dymczykm/7909_dcdc_converter/ltspice/lt3471.asc

C1: cap; 22µ; Rser=0 Lser=0 mfg="Murata" pn="GCM32ER71C226ME19" type="X7R"
C2: cap; 100n; Rser=16.9m Lser=332p mfg="Würth Elektronik" pn="885012205037 WCAP-CSGP 0402" type="X7R"
C3: cap; 22µ; Rser=0 Lser=0 mfg="Murata" pn="GCM32ER71C226ME19" type="X7R"
C4: cap; 22µ; Rser=0 Lser=0 mfg="Murata" pn="GCM32ER71C226ME19" type="X7R"
C5: cap; 150p; Rser=110.8m Lser=560p mfg="Würth Elektronik" pn="885012006024 WCAP-CSGP 0603" type="NP0"
C6: cap; 22µ; Rser=0 Lser=0 mfg="Murata" pn="GCM32ER71C226ME19" type="X7R"
C7: cap; 10n; Rser=55.4m Lser=199p mfg="Würth Elektronik" pn="885012205031 WCAP-CSGP 0402" type="X7R"
C8: cap; 22µ; Rser=0 Lser=0 mfg="Murata" pn="GCM32ER71C226ME19" type="X7R"
C9: cap; 150p; Rser=110.8m Lser=560p mfg="Würth Elektronik" pn="885012006024 WCAP-CSGP 0603" type="NP0"
C10: cap; 22µ; Rser=0 Lser=0 mfg="Murata" pn="GCM32ER71C226ME19" type="X7R"
C11: cap; 10n; Rser=55.4m Lser=199p mfg="Würth Elektronik" pn="885012205031 WCAP-CSGP 0402" type="X7R"
D1: schottky; MBRS130L
D2: schottky; MBRS130L
L1: ind; 10µ; Ipk=3 Rser=84m Rpar=942 Cpar=0 mfg="Coilcraft" pn="XAL4040-103"
L2: ind; 33µ; Ipk=1.2 Rser=223.6m Rpar=3.109K Cpar=0 mfg="Coilcraft" pn="LPS6225-333"
L3: ind; 33µ; Ipk=1.2 Rser=223.6m Rpar=3.109K Cpar=0 mfg="Coilcraft" pn="LPS6225-333"
L4: ind; 33µ; Ipk=1.2 Rser=223.6m Rpar=3.109K Cpar=0 mfg="Coilcraft" pn="LPS6225-333"
L5: ind; 22µ; Ipk=970m Rser=156.52m Rpar=2.072K Cpar=0 mfg="Coilcraft" pn="MOS6020-223"
L6: ind; 15µ; Ipk=2.8 Rser=109m Rpar=1.413K Cpar=0 mfg="Coilcraft" pn="XAL4040-153"
L7: ind; 33µ; Ipk=1.2 Rser=223.6m Rpar=3.109K Cpar=0 mfg="Coilcraft" pn="LPS6225-333"
R1: res; 20k
R2: res; 22k
R3: res; 2k05
R4: res; 2k05
R5: res; 135
R6: res; 95
U1: LT3471
V1: voltage; 13.6
Named nets: 0, +10V, -10V, VIN
.tran 0 3m 2m
